Krisstank/Ender_3_Pro_v2_Max_SW_conversion/DXF/BLACK/top_rear_panel.dxf

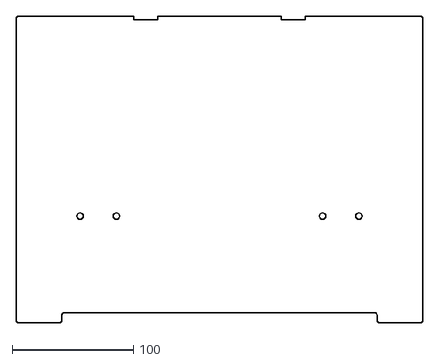
[picture p18: CAD file, 2023-01-02]
DXF/BLACK/top_rear_panel.dxf
336.0 x 253.0
