Krisstank/Ender_3_Pro_v2_Max_SW_conversion/DXF/CLEAR/front_side_clear_x2.dxf

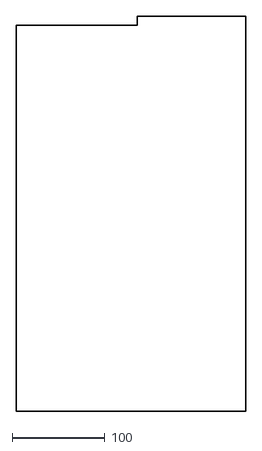
[picture p19: CAD file, 2023-01-02]
DXF/CLEAR/front_side_clear_x2.dxf
247.0 x 426.0
