Krisstank/Ender_3_Pro_v2_Max_SW_conversion/STL/Electronics/LCD/Mini12864/mount_mini12864.stl

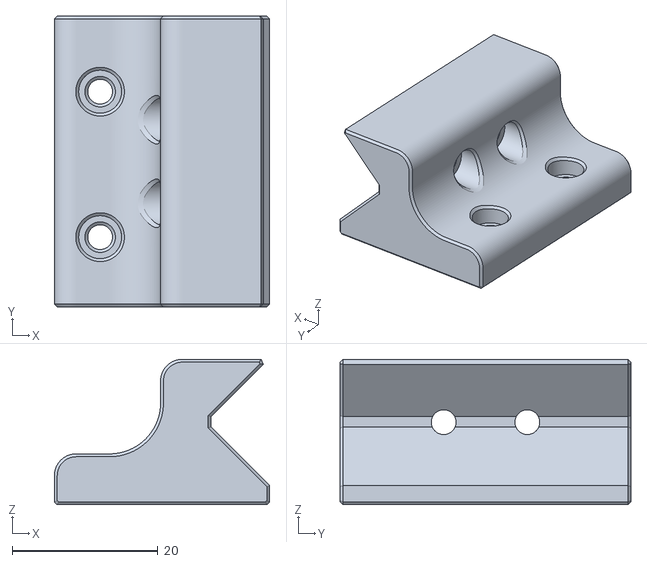
[picture p20: CAD file, 2023-01-02]
STL/Electronics/LCD/Mini12864/mount_mini12864.stl
29.6 x 40.0 x 20.0
