Krisstank/Ender_3_Pro_v2_Max_SW_conversion/STL/Electronics/rpi3_mount.stl

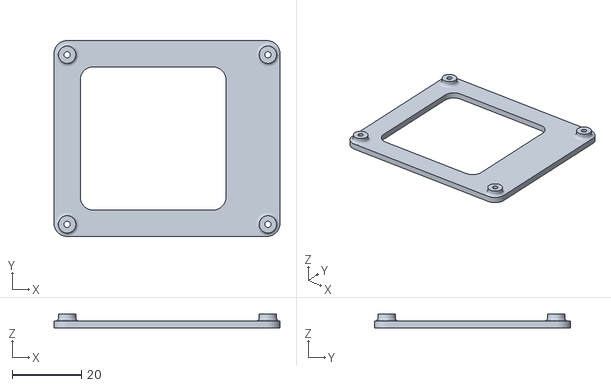
[picture p21: CAD file, 2023-01-02]
STL/Electronics/rpi3_mount.stl
65.3 x 56.6 x 4.00
