Krisstank/Ender_3_Pro_v2_Max_SW_conversion/STL/Gantry/XZ_Axis/XZ_Axis_Max/x_motor_mount_a_max.stl

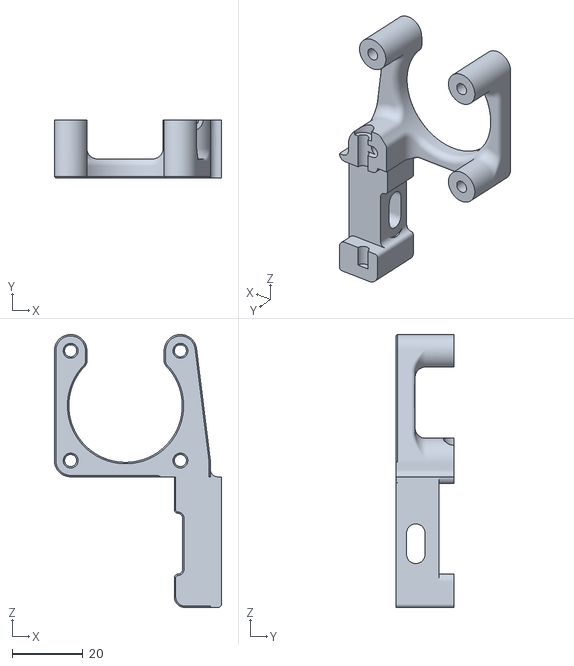
[picture p22: CAD file, 2023-01-02]
STL/Gantry/XZ_Axis/XZ_Axis_Max/x_motor_mount_a_max.stl
47.2 x 16.4 x 77.1
