Krisstank/Ender_3_Pro_v2_Max_SW_conversion/STL/Gantry/XZ_Axis/xz_block_right_b.stl

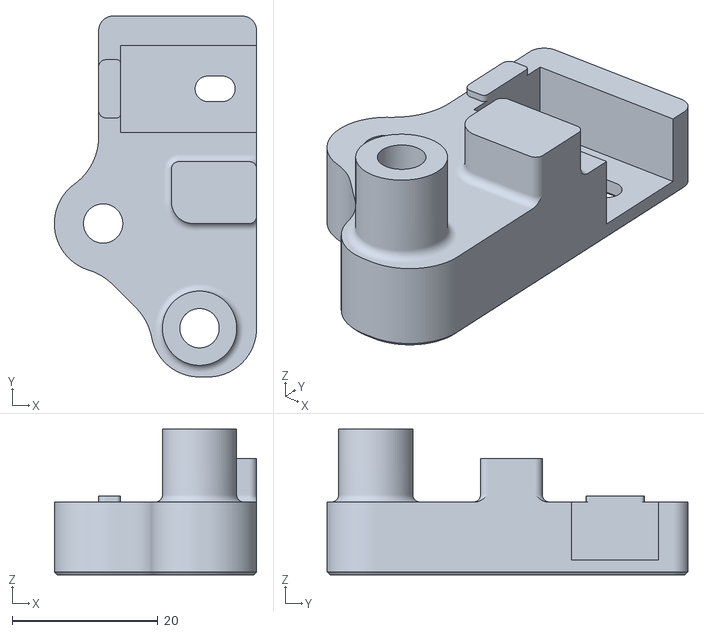
[picture p23: CAD file, 2023-01-02]
STL/Gantry/XZ_Axis/xz_block_right_b.stl
27.8 x 49.6 x 20.0
