Krisstank/Ender_3_Pro_v2_Max_SW_conversion/STL/Gantry/Y_Axis/[a]_y_chain_frame_mount_igus.stl

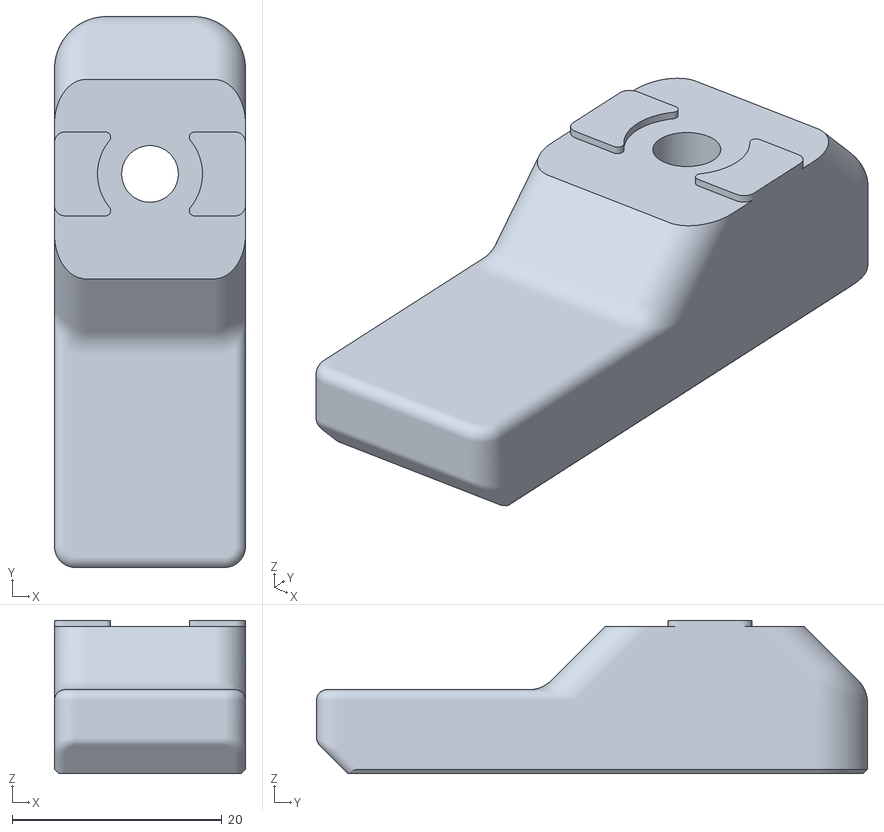
[picture p24: CAD file, 2023-01-02]
STL/Gantry/Y_Axis/[a]_y_chain_frame_mount_igus.stl
18.2 x 52.5 x 14.6
