Krisstank/Ender_3_Pro_v2_Max_SW_conversion/STL/Grills/[a]_grill_endcap_x4.stl

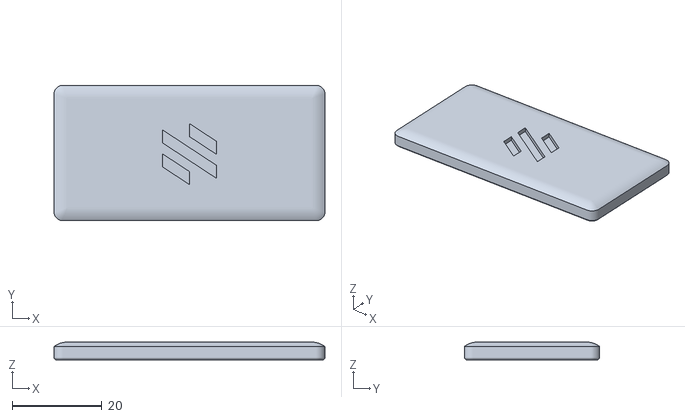
[picture p25: CAD file, 2023-01-02]
STL/Grills/[a]_grill_endcap_x4.stl
60.4 x 30.2 x 4.00
