Krisstank/Ender_3_Pro_v2_Max_SW_conversion/STL/Panel_Mounting/Doors/door_hinge_x4.stl

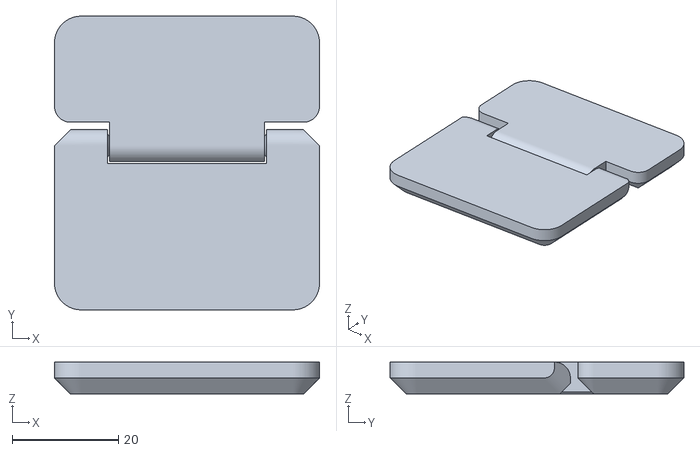
[picture p26: CAD file, 2023-01-02]
STL/Panel_Mounting/Doors/door_hinge_x4.stl
50.0 x 55.4 x 6.00
