Krisstank/Ender_3_Pro_v2_Max_SW_conversion/STL/Panel_Mounting/front_panel_bracket_a_x2.stl

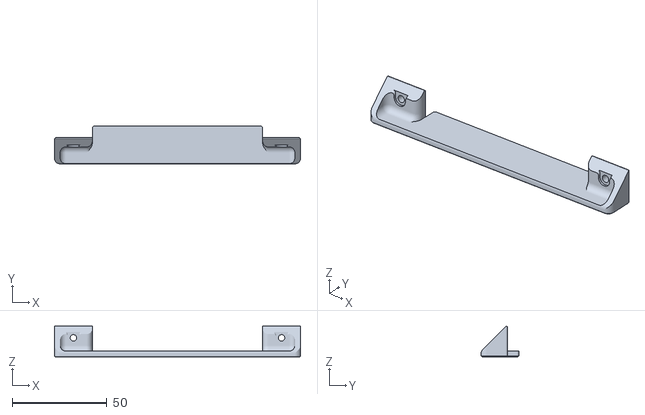
[picture p27: CAD file, 2023-01-02]
STL/Panel_Mounting/front_panel_bracket_a_x2.stl
130.0 x 20.0 x 16.2
