Krisstank/Ender_3_Pro_v2_Max_SW_conversion/STL/spool_holder.stl

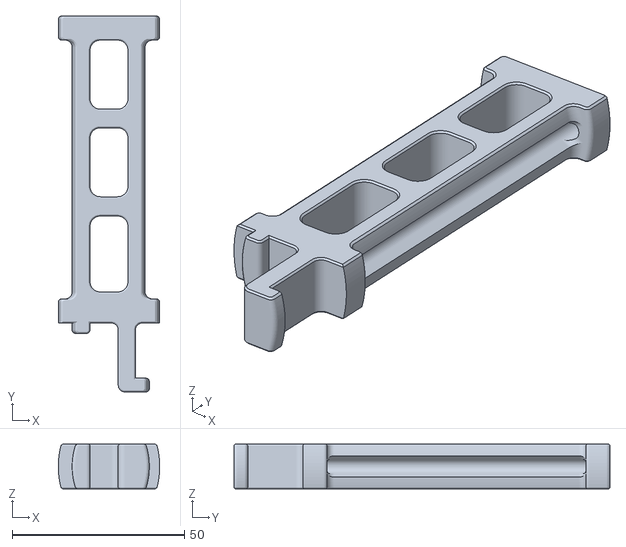
[picture p28: CAD file, 2023-01-02]
STL/spool_holder.stl
29.4 x 109.0 x 13.0
