Krisstank/Ender_3_Pro_v2_Max_SW_conversion/DXF/BLACK/rear_side_panel_x2.dxf

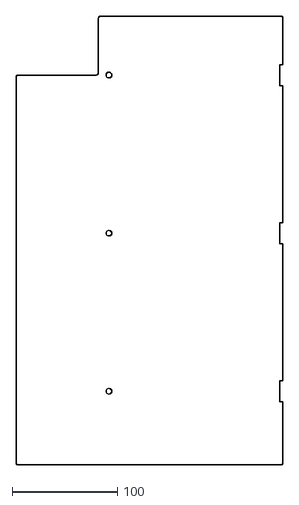
[picture p29: CAD file, 2023-01-02]
DXF/BLACK/rear_side_panel_x2.dxf
253.0 x 426.0
