Krisstank/Ender_3_Pro_v2_Max_SW_conversion/DXF/CLEAR/front_clear_door_x2.dxf

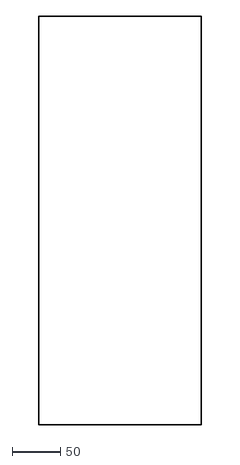
[picture p30: CAD file, 2023-01-02]
DXF/CLEAR/front_clear_door_x2.dxf
168.0 x 422.0
