Krisstank/Ender_3_Pro_v2_Max_SW_conversion/STL/Decks/front_left.stl

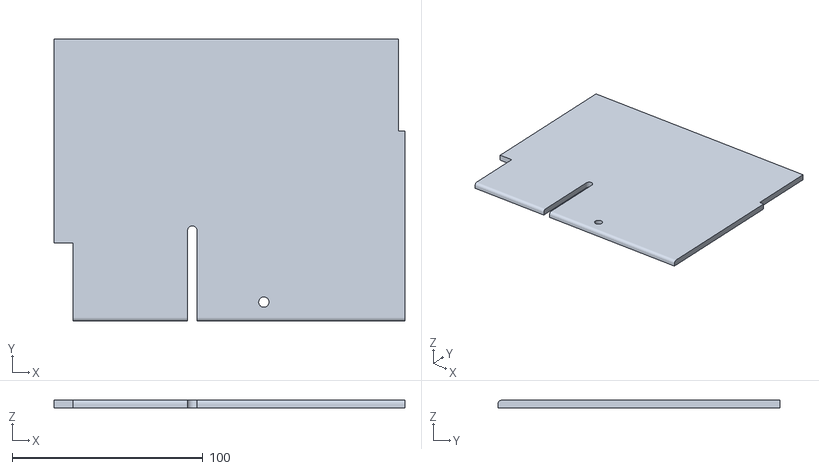
[picture p31: CAD file, 2023-01-02]
STL/Decks/front_left.stl
184.0 x 148.0 x 4.00
