Krisstank/Ender_3_Pro_v2_Max_SW_conversion/STL/Electronics/LCD/Mini12864/lcd_case_rear_mini12864.stl

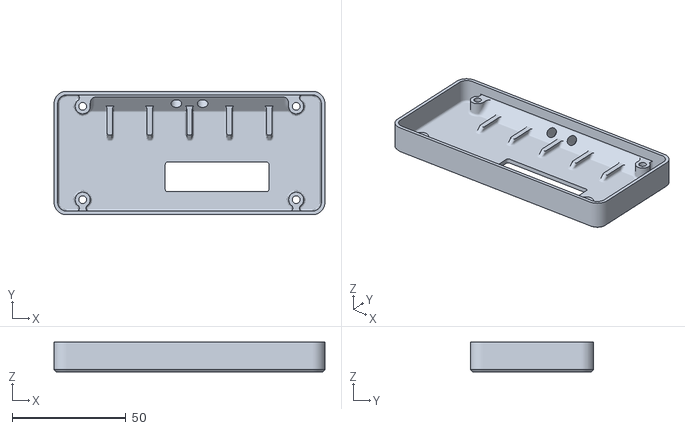
[picture p32: CAD file, 2023-01-02]
STL/Electronics/LCD/Mini12864/lcd_case_rear_mini12864.stl
119.0 x 54.2 x 13.0
