Krisstank/Ender_3_Pro_v2_Max_SW_conversion/STL/Electronics/PS_4040_mount_b.stl

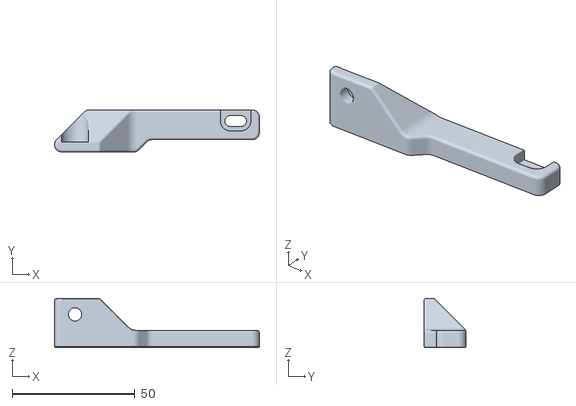
[picture p33: CAD file, 2023-01-02]
STL/Electronics/PS_4040_mount_b.stl
83.4 x 17.1 x 20.0
