Krisstank/Ender_3_Pro_v2_Max_SW_conversion/STL/foot_tpu_x4.stl

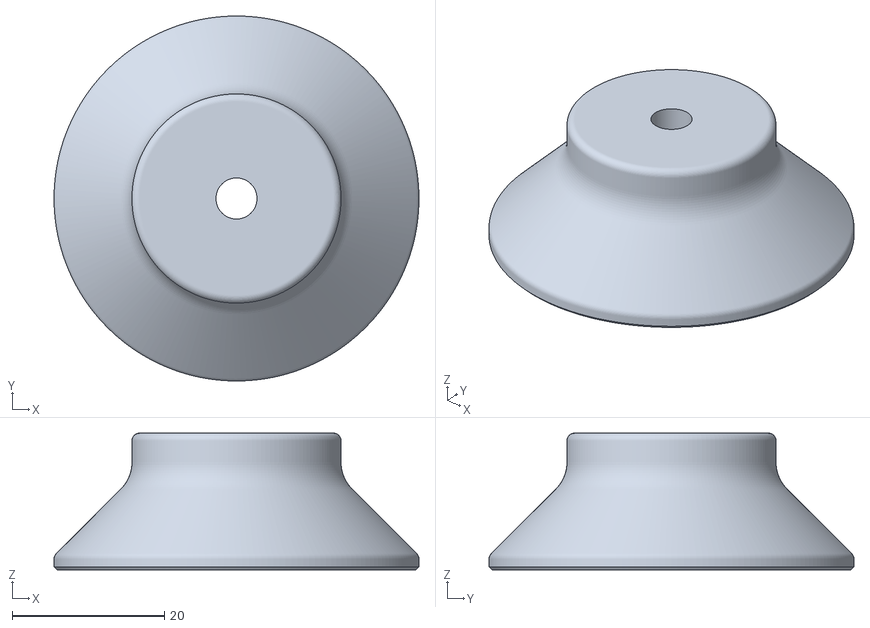
[picture p34: CAD file, 2023-01-02]
STL/foot_tpu_x4.stl
48.0 x 48.0 x 18.0
