Krisstank/Ender_3_Pro_v2_Max_SW_conversion/STL/Gantry/XZ_Axis/keybak_idler_bracket.stl

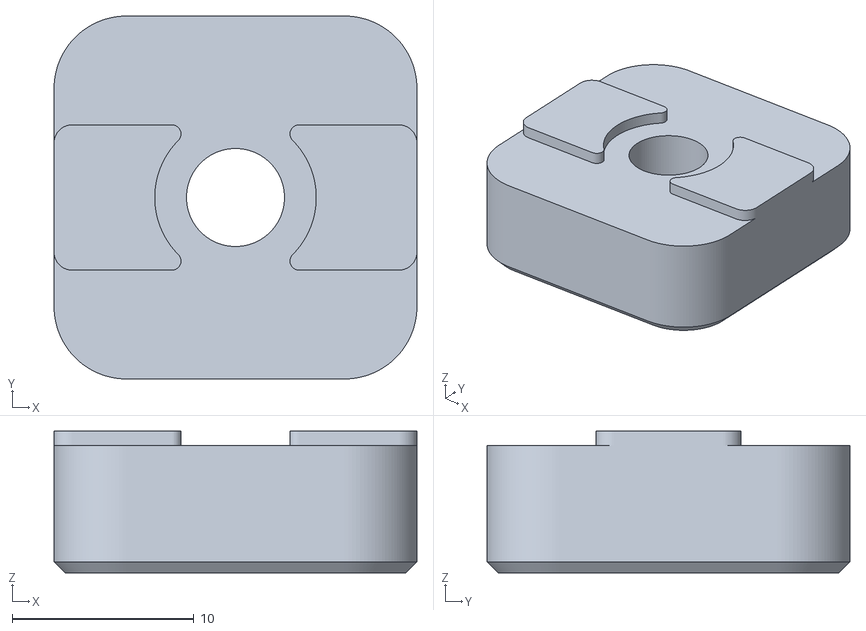
[picture p35: CAD file, 2023-01-02]
STL/Gantry/XZ_Axis/keybak_idler_bracket.stl
20.0 x 20.0 x 7.80
