Krisstank/Ender_3_Pro_v2_Max_SW_conversion/STL/Gantry/XZ_Axis/XZ_Axis_Max/z_motor_mount_b_max.stl

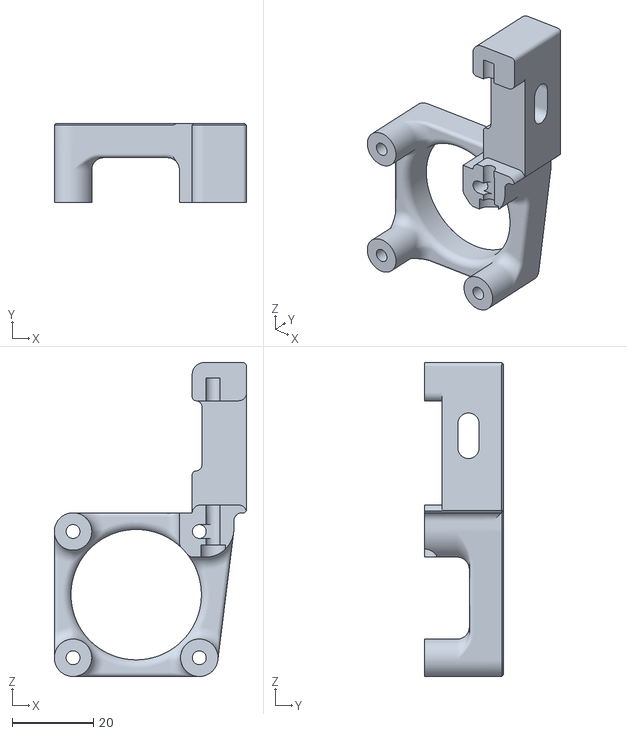
[picture p36: CAD file, 2023-01-02]
STL/Gantry/XZ_Axis/XZ_Axis_Max/z_motor_mount_b_max.stl
47.2 x 19.4 x 77.1
