Krisstank/Ender_3_Pro_v2_Max_SW_conversion/STL/Gantry/Y_Axis/[a]_y_idler_outter.stl

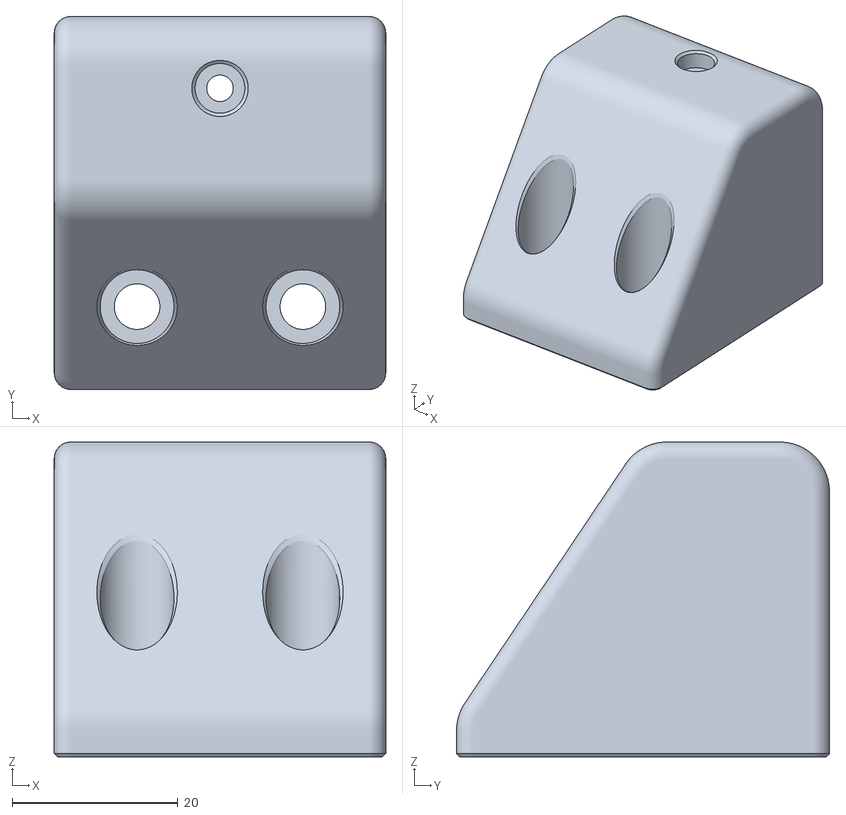
[picture p37: CAD file, 2023-01-02]
STL/Gantry/Y_Axis/[a]_y_idler_outter.stl
40.0 x 45.0 x 38.0
