Krisstank/Ender_3_Pro_v2_Max_SW_conversion/STL/Grills/grill_front_middle.stl

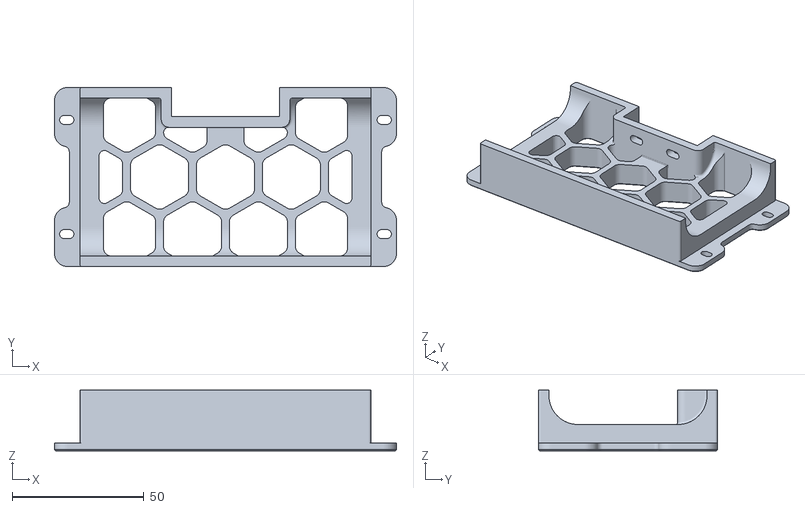
[picture p38: CAD file, 2023-01-02]
STL/Grills/grill_front_middle.stl
129.8 x 68.0 x 23.0
