Krisstank/Ender_3_Pro_v2_Max_SW_conversion/STL/Panel_Mounting/panel_clip_x4.stl

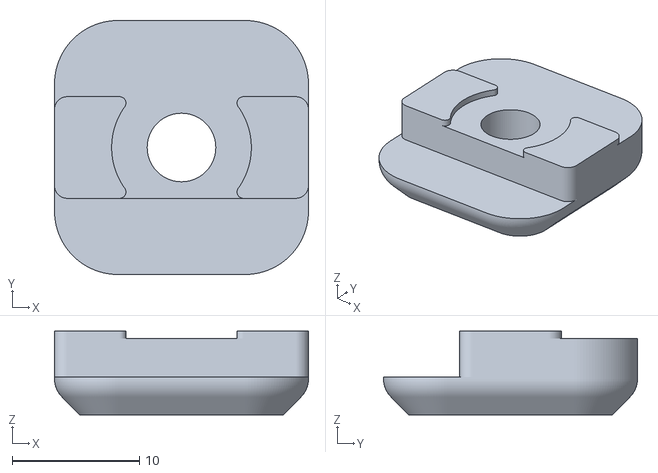
[picture p39: CAD file, 2023-01-02]
STL/Panel_Mounting/panel_clip_x4.stl
20.0 x 20.0 x 6.60
