Krisstank/Ender_3_Pro_v2_Max_SW_conversion/DXF/BLACK/deck_right.dxf

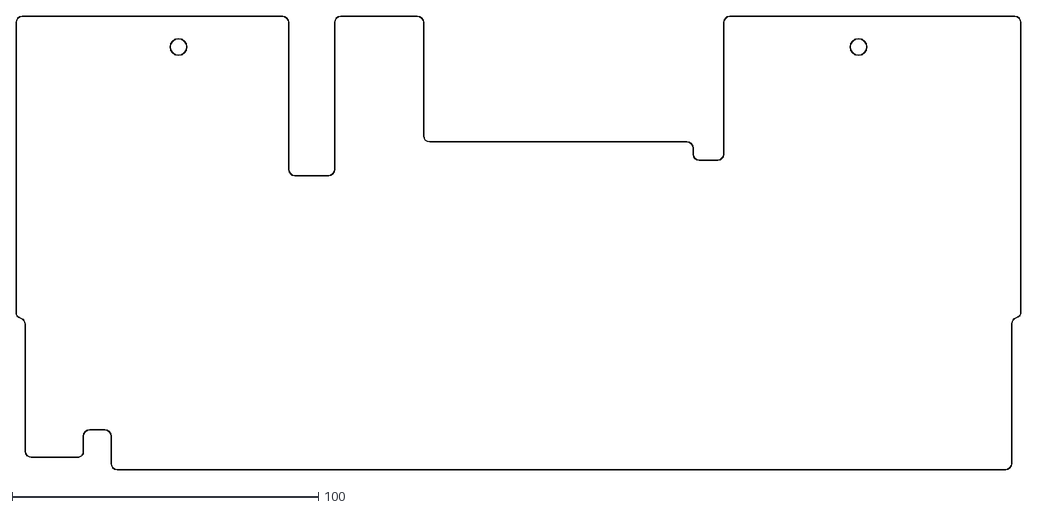
[picture p40: CAD file, 2023-01-02]
DXF/BLACK/deck_right.dxf
328.0 x 148.0
