Krisstank/Ender_3_Pro_v2_Max_SW_conversion/STL/Gantry/XZ_Axis/[a]_upper_idler_support_b_right.stl

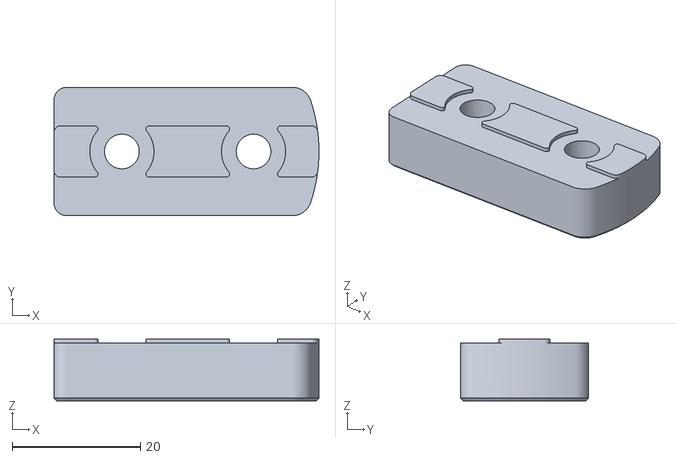
[picture p42: CAD file, 2023-01-02]
STL/Gantry/XZ_Axis/[a]_upper_idler_support_b_right.stl
41.3 x 20.0 x 9.60
