Krisstank/Ender_3_Pro_v2_Max_SW_conversion/STL/Gantry/Y_Axis/[a]_y_chain_bed_mount_generic.stl

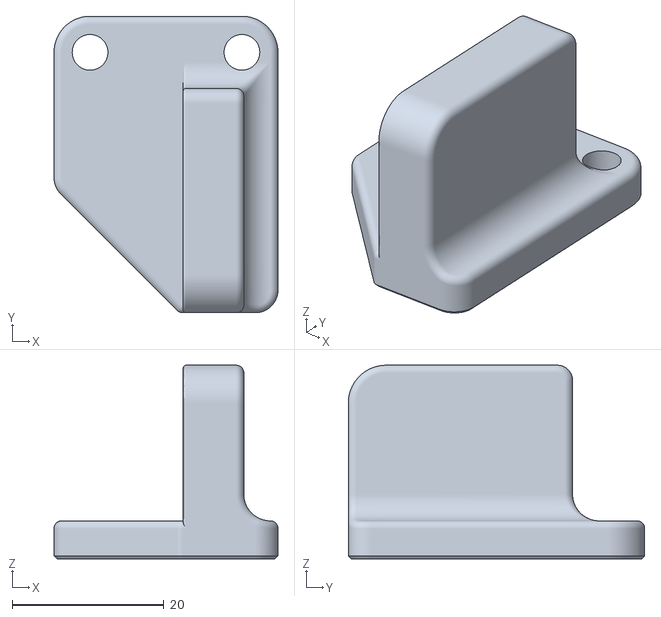
[picture p43: CAD file, 2023-01-02]
STL/Gantry/Y_Axis/[a]_y_chain_bed_mount_generic.stl
29.5 x 39.0 x 25.5
