Krisstank/Ender_3_Pro_v2_Max_SW_conversion/STL/Panel_Mounting/rear_panel_bracket_x5.stl

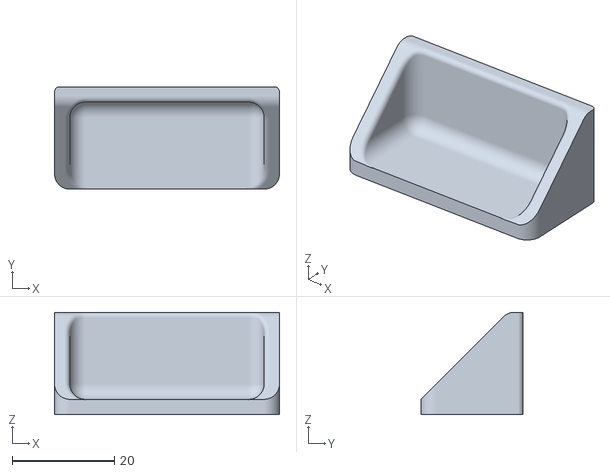
[picture p44: CAD file, 2023-01-02]
STL/Panel_Mounting/rear_panel_bracket_x5.stl
44.0 x 20.0 x 20.0
