Krisstank/Ender_3_Pro_v2_Max_SW_conversion/DXF/BLACK/rear_panel.dxf

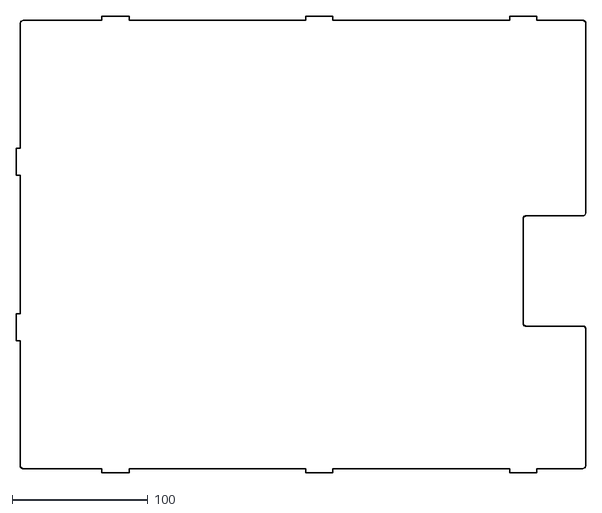
[picture p45: CAD file, 2023-01-02]
DXF/BLACK/rear_panel.dxf
419.0 x 336.0
