Krisstank/Ender_3_Pro_v2_Max_SW_conversion/STL/Electronics/rpi3_shelf.stl

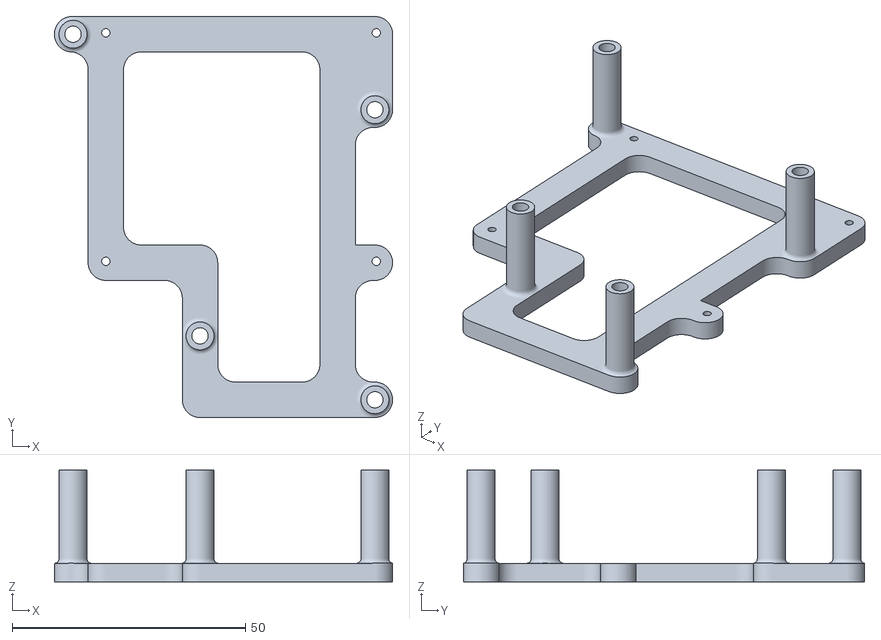
[picture p46: CAD file, 2023-01-02]
STL/Electronics/rpi3_shelf.stl
72.5 x 86.0 x 24.0
