Krisstank/Ender_3_Pro_v2_Max_SW_conversion/STL/frame_extension_x2_max.stl

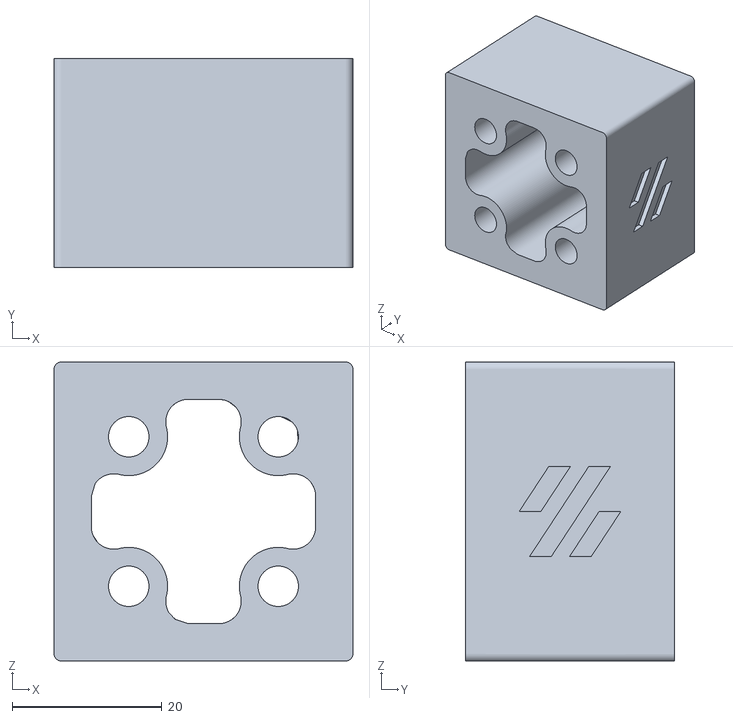
[picture p47: CAD file, 2023-01-02]
STL/frame_extension_x2_max.stl
40.0 x 28.0 x 40.0
