Krisstank/Ender_3_Pro_v2_Max_SW_conversion/STL/Gantry/XZ_Axis/[a]_xz_cable_cover.stl

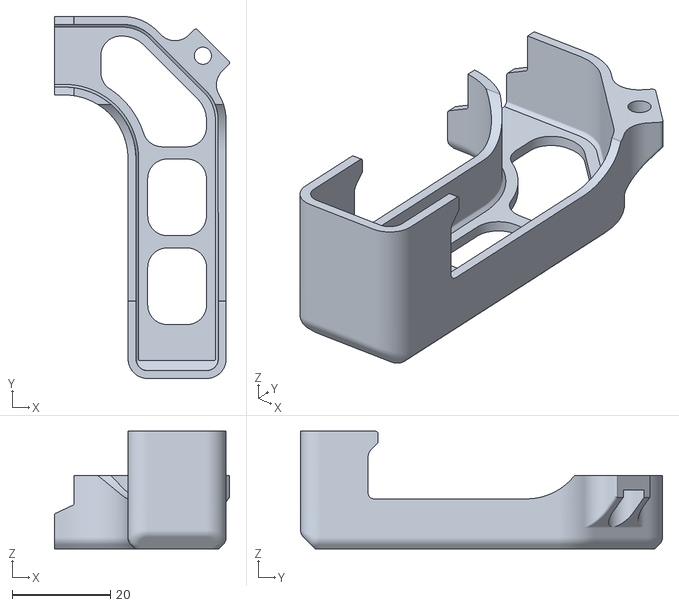
[picture p48: CAD file, 2023-01-02]
STL/Gantry/XZ_Axis/[a]_xz_cable_cover.stl
35.7 x 73.8 x 24.0
