Krisstank/Ender_3_Pro_v2_Max_SW_conversion/STL/Gantry/Y_Axis/[a]_y_axis_ls_mount.stl

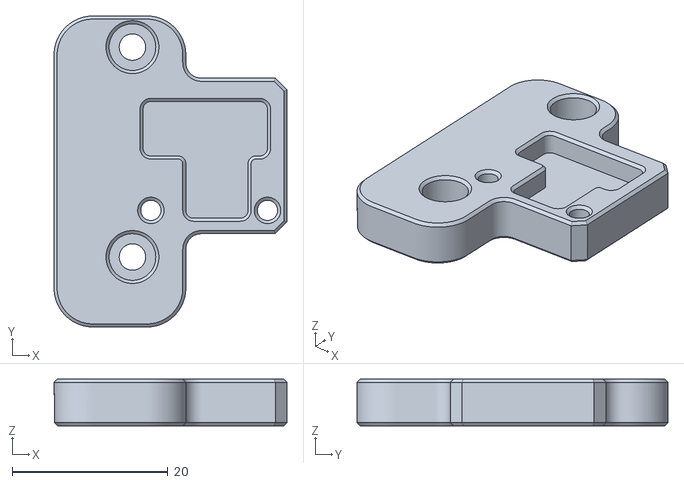
[picture p49: CAD file, 2023-01-02]
STL/Gantry/Y_Axis/[a]_y_axis_ls_mount.stl
30.0 x 40.0 x 6.00
