Krisstank/Ender_3_Pro_v2_Max_SW_conversion/STL/Grills/grill_rear_right.stl

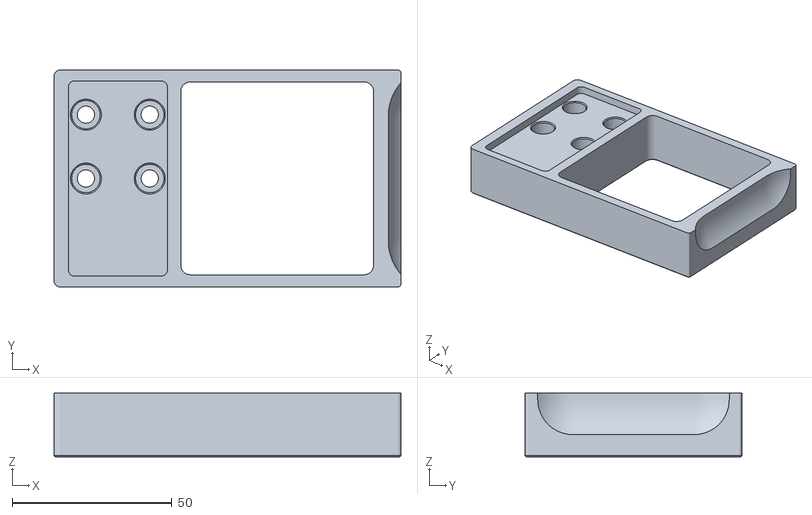
[picture p50: CAD file, 2023-01-02]
STL/Grills/grill_rear_right.stl
108.7 x 68.0 x 20.0
