Krisstank/Ender_3_Pro_v2_Max_SW_conversion/DXF/BLACK/front_bottom_panel.dxf

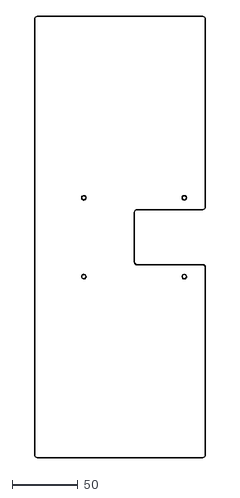
[picture p52: CAD file, 2023-01-02]
DXF/BLACK/front_bottom_panel.dxf
130.0 x 336.0
