Krisstank/Ender_3_Pro_v2_Max_SW_conversion/STL/Electronics/rs_25_mount.stl

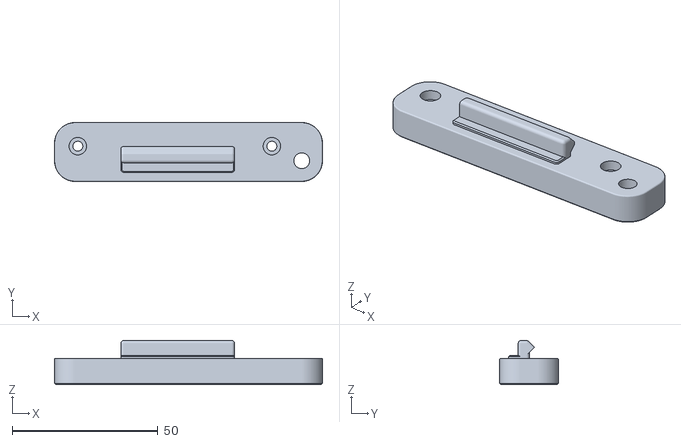
[picture p53: CAD file, 2023-01-02]
STL/Electronics/rs_25_mount.stl
91.9 x 20.2 x 15.1
