Krisstank/Ender_3_Pro_v2_Max_SW_conversion/STL/Gantry/Y_Axis/[a]_y_belt_clip_x2.stl

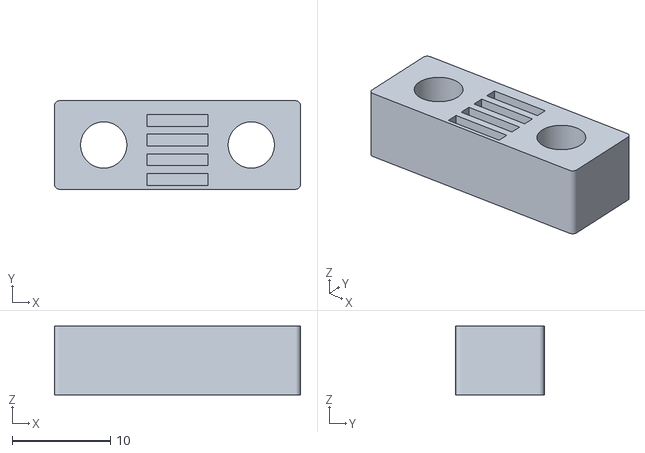
[picture p55: CAD file, 2023-01-02]
STL/Gantry/Y_Axis/[a]_y_belt_clip_x2.stl
25.0 x 9.00 x 7.00
