Krisstank/Ender_3_Pro_v2_Max_SW_conversion/STL/Panel_Mounting/front_bottom_panel_bracket.stl

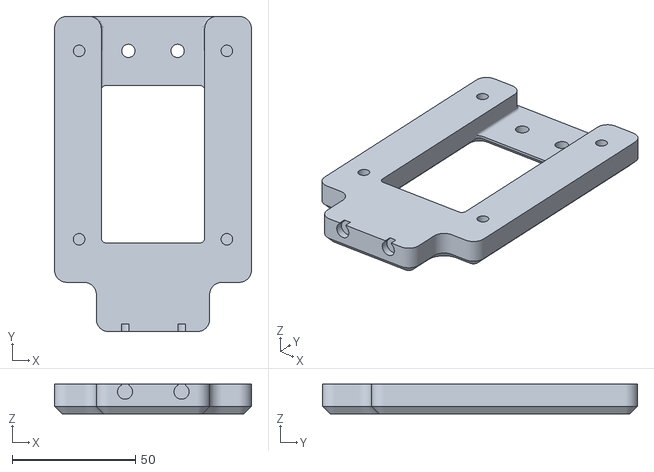
[picture p56: CAD file, 2023-01-02]
STL/Panel_Mounting/front_bottom_panel_bracket.stl
80.0 x 128.0 x 12.0
