Krisstank/Ender_3_Pro_v2_Max_SW_conversion/STL/spool_holder_base.stl

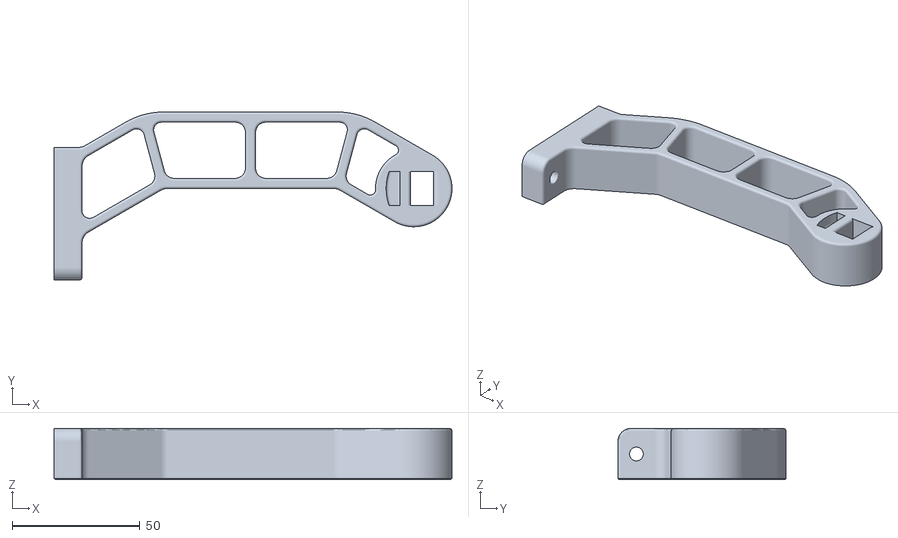
[picture p57: CAD file, 2023-01-02]
STL/spool_holder_base.stl
156.0 x 65.9 x 20.0
