Krisstank/Ender_3_Pro_v2_Max_SW_conversion/STL/Electronics/skr_mini_e3_mount.stl

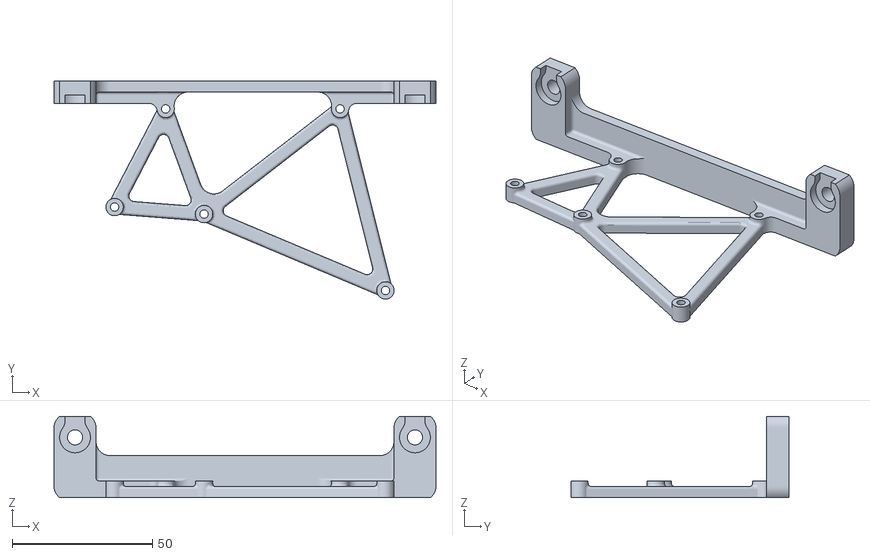
[picture p58: CAD file, 2023-01-02]
STL/Electronics/skr_mini_e3_mount.stl
136.2 x 77.8 x 29.0
