Krisstank/Ender_3_Pro_v2_Max_SW_conversion/STL/foot_extention_x4.stl

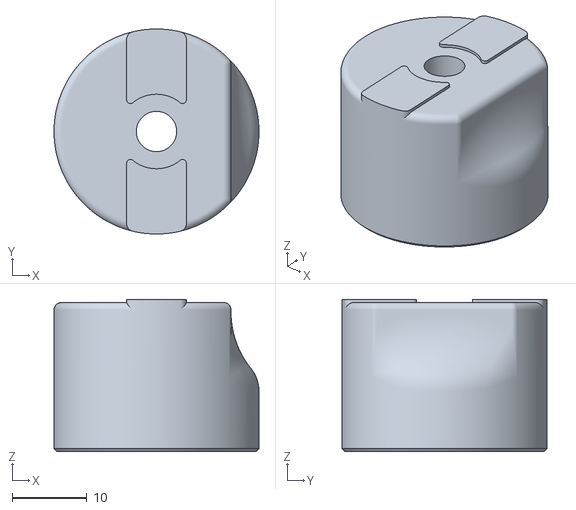
[picture p59: CAD file, 2023-01-02]
STL/foot_extention_x4.stl
27.5 x 27.5 x 20.4
