Krisstank/Ender_3_Pro_v2_Max_SW_conversion/STL/Gantry/XZ_Axis/z_bearing_block_left.stl

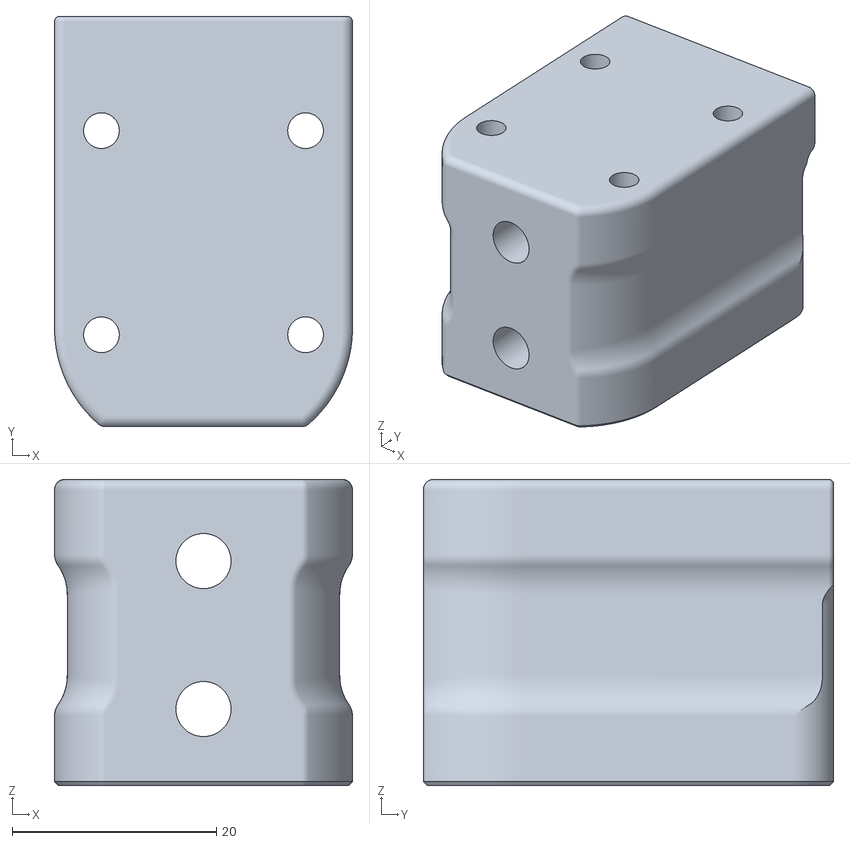
[picture p60: CAD file, 2023-01-02]
STL/Gantry/XZ_Axis/z_bearing_block_left.stl
29.2 x 40.2 x 30.0
