Krisstank/Ender_3_Pro_v2_Max_SW_conversion/STL/Gantry/Y_Axis/[a]_y_idler_inner.stl

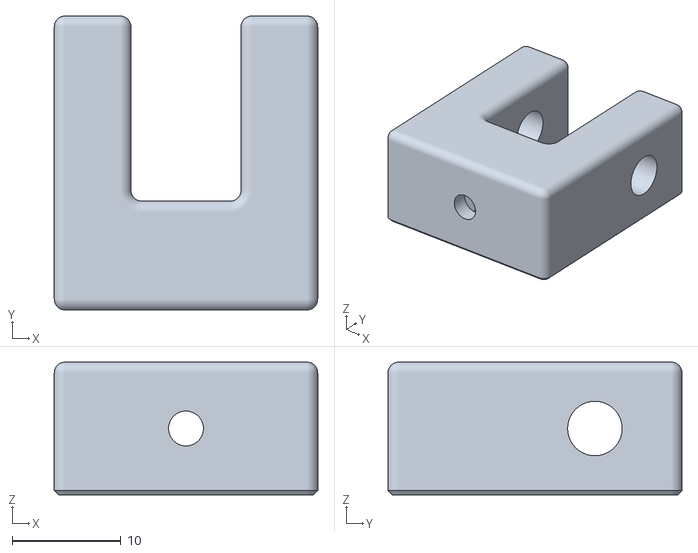
[picture p61: CAD file, 2023-01-02]
STL/Gantry/Y_Axis/[a]_y_idler_inner.stl
24.2 x 27.0 x 12.2
