Krisstank/Ender_3_Pro_v2_Max_SW_conversion/STL/Panel_Mounting/light_bar_x2.stl

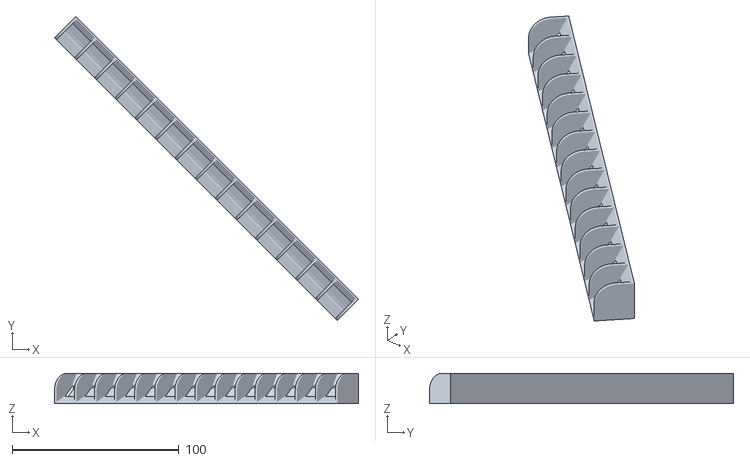
[picture p62: CAD file, 2023-01-02]
STL/Panel_Mounting/light_bar_x2.stl
182.2 x 182.2 x 18.0
