Krisstank/Ender_3_Pro_v2_Max_SW_conversion/STL/cover_4040_extrusion_cut_enderV2.stl

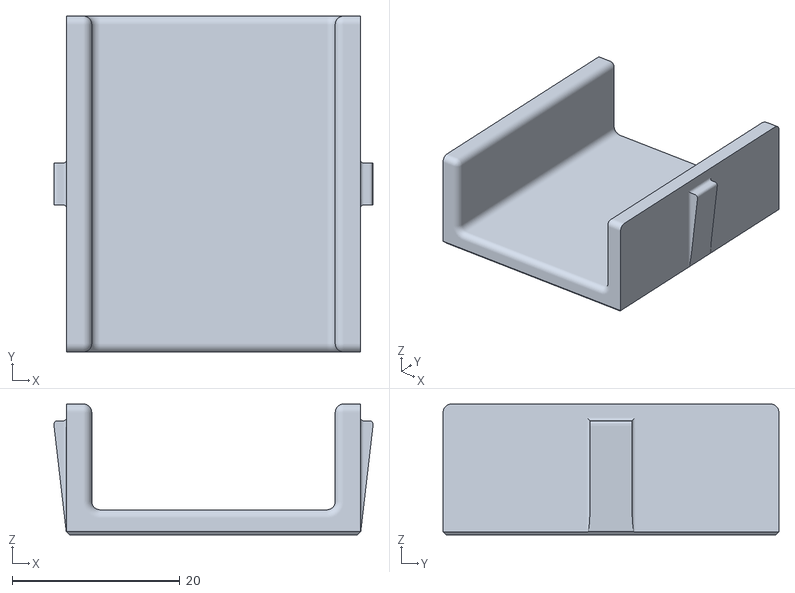
[picture p63: CAD file, 2023-01-02]
STL/cover_4040_extrusion_cut_enderV2.stl
38.0 x 40.0 x 15.6
