Krisstank/Ender_3_Pro_v2_Max_SW_conversion/STL/Gantry/Y_Axis/y_motor_mount_a.stl

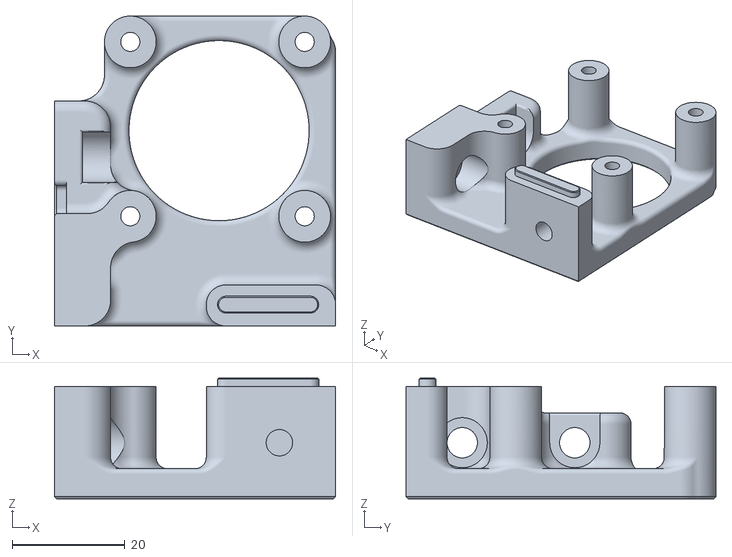
[picture p65: CAD file, 2023-01-02]
STL/Gantry/Y_Axis/y_motor_mount_a.stl
50.0 x 55.1 x 21.5
