Krisstank/Ender_3_Pro_v2_Max_SW_conversion/STL/Panel_Mounting/panel_clip_wide_x2.stl

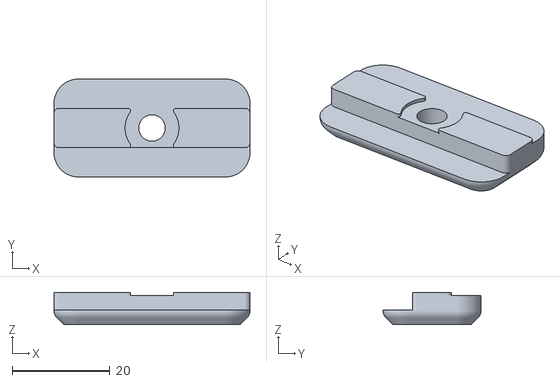
[picture p66: CAD file, 2023-01-02]
STL/Panel_Mounting/panel_clip_wide_x2.stl
40.0 x 20.0 x 6.60
