Krisstank/Ender_3_Pro_v2_Max_SW_conversion/STL/Gantry/XZ_Axis/z_carriage_stop_bottom_x2.stl

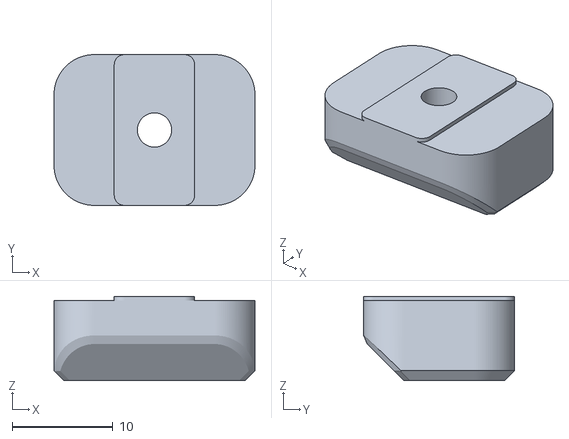
[picture p67: CAD file, 2023-01-02]
STL/Gantry/XZ_Axis/z_carriage_stop_bottom_x2.stl
20.0 x 15.0 x 8.40
