Krisstank/Ender_3_Pro_v2_Max_SW_conversion/STL/Panel_Mounting/top_door_latch.stl

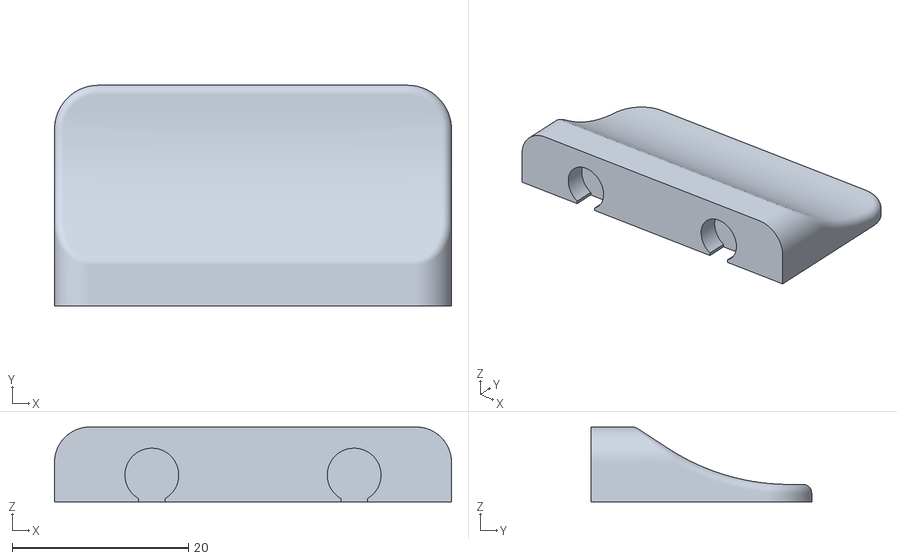
[picture p69: CAD file, 2023-01-02]
STL/Panel_Mounting/top_door_latch.stl
45.0 x 25.0 x 8.50
