Krisstank/Ender_3_Pro_v2_Max_SW_conversion/STL/Gantry/Y_Axis/y_axis_Ender3_Max_CR10_bed_carriage.stl

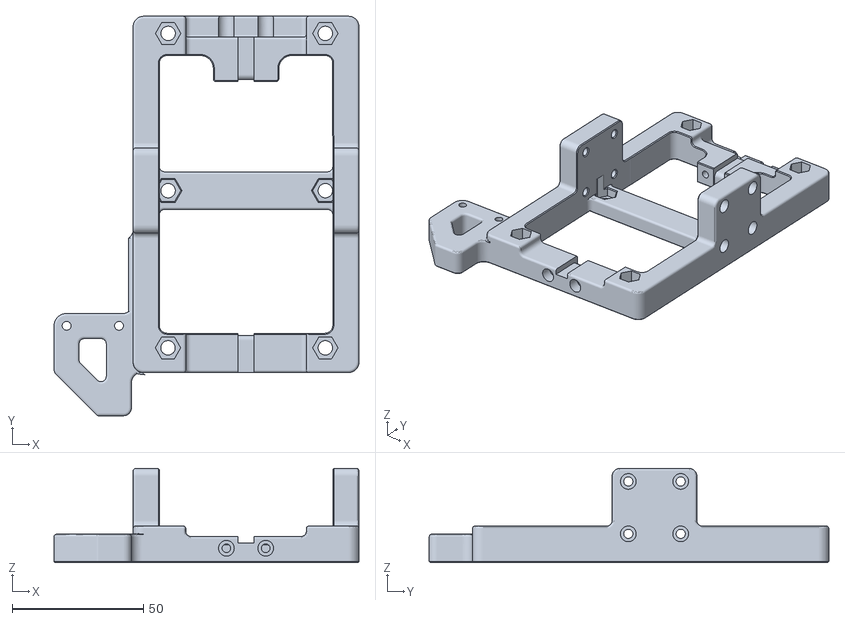
[picture p70: CAD file, 2023-01-02]
STL/Gantry/Y_Axis/y_axis_Ender3_Max_CR10_bed_carriage.stl
116.4 x 152.5 x 36.0
