Krisstank/Ender_3_Pro_v2_Max_SW_conversion/STL/Panel_Mounting/feed_slot.stl

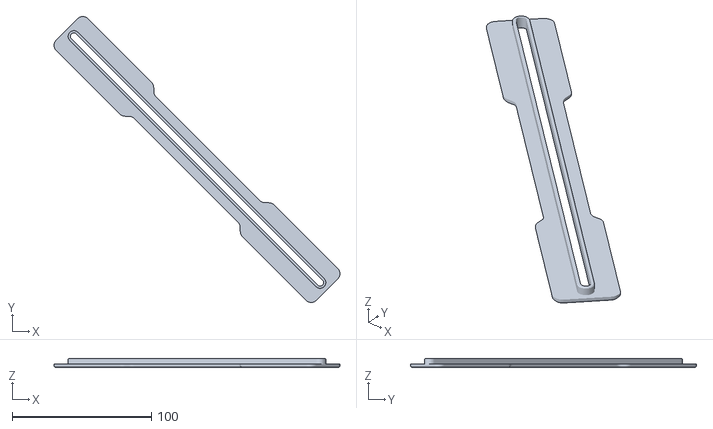
[picture p71: CAD file, 2023-01-02]
STL/Panel_Mounting/feed_slot.stl
205.3 x 205.3 x 6.40
