Krisstank/Ender_3_Pro_v2_Max_SW_conversion/STL/Gantry/Y_Axis/y_motor_mount_b.stl

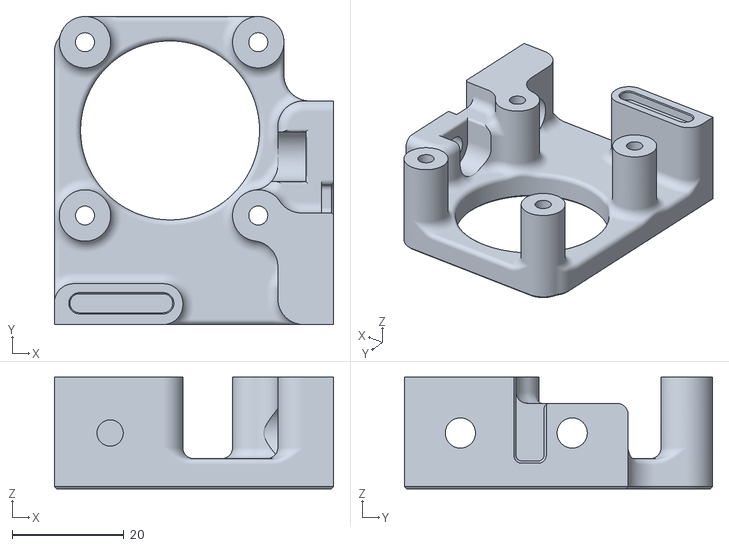
[picture p72: CAD file, 2023-01-02]
STL/Gantry/Y_Axis/y_motor_mount_b.stl
50.0 x 55.1 x 20.0
