Krisstank/Ender_3_Pro_v2_Max_SW_conversion/STL/Gantry/XZ_Axis/keybak_mount.stl

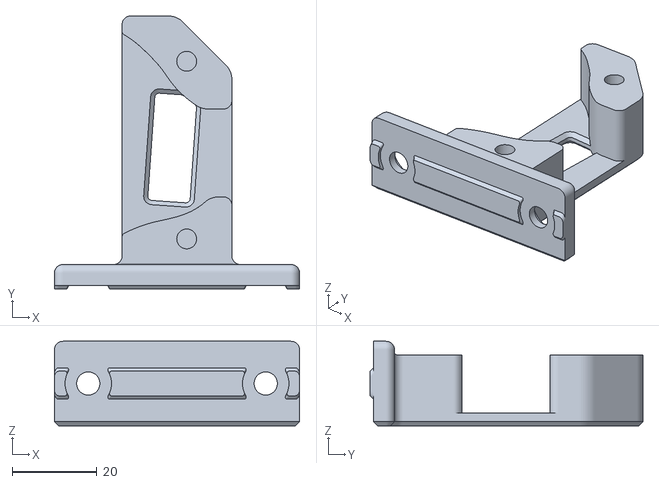
[picture p73: CAD file, 2023-01-02]
STL/Gantry/XZ_Axis/keybak_mount.stl
58.0 x 64.6 x 20.0
