Krisstank/Ender_3_Pro_v2_Max_SW_conversion/STL/Gantry/Y_Axis/y_axis_bed_carriage.stl

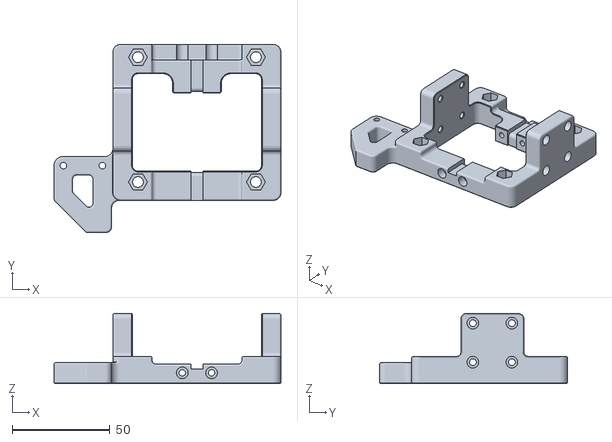
[picture p74: CAD file, 2023-01-02]
STL/Gantry/Y_Axis/y_axis_bed_carriage.stl
116.4 x 96.5 x 36.0
