Krisstank/Ender_3_Pro_v2_Max_SW_conversion/STL/Gantry/XZ_Axis/x_motor_mount_b.stl

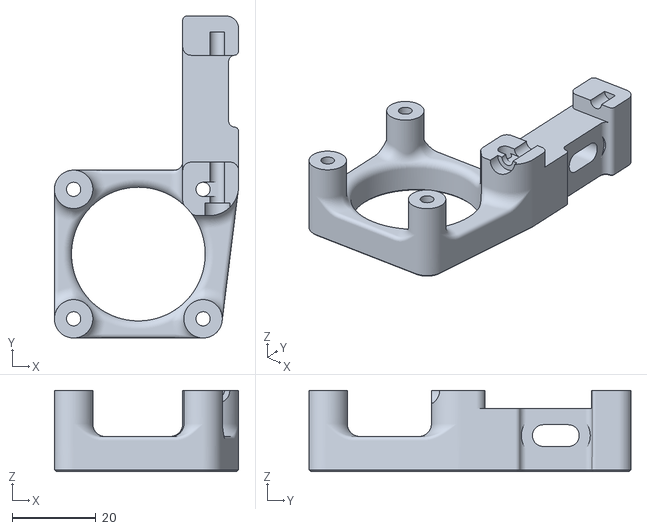
[picture p75: CAD file, 2023-01-02]
STL/Gantry/XZ_Axis/x_motor_mount_b.stl
44.1 x 77.1 x 19.4
