Krisstank/Ender_3_Pro_v2_Max_SW_conversion/STL/Gantry/XZ_Axis/z_bearing_block_right_igus.stl

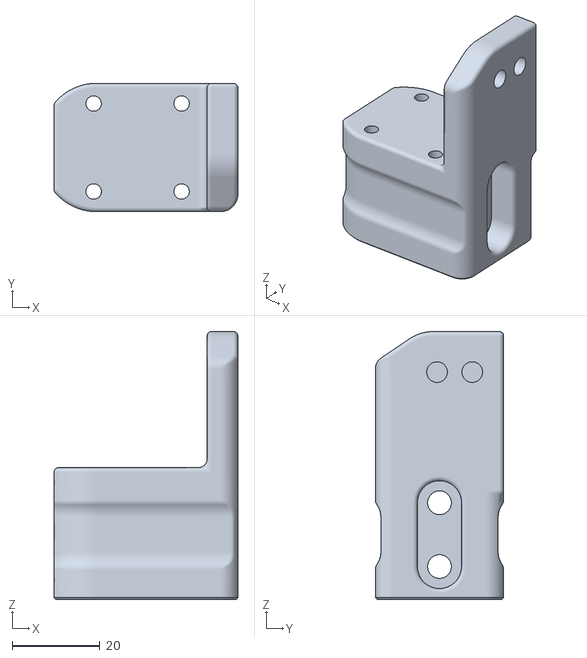
[picture p77: CAD file, 2023-01-02]
STL/Gantry/XZ_Axis/z_bearing_block_right_igus.stl
41.8 x 29.2 x 60.9
