Krisstank/Ender_3_Pro_v2_Max_SW_conversion/STL/Gantry/XZ_Axis/[a]_z_chain_lower_mount_generic.stl

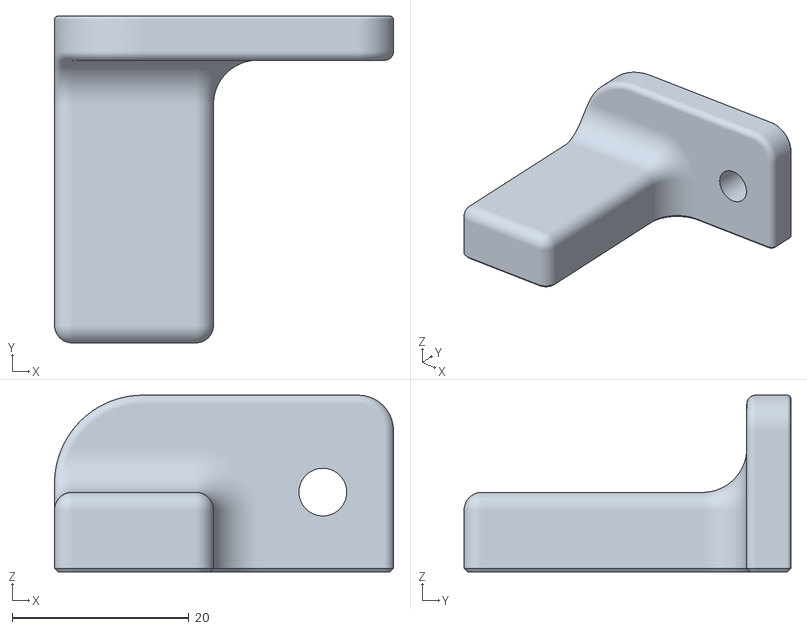
[picture p78: CAD file, 2023-01-02]
STL/Gantry/XZ_Axis/[a]_z_chain_lower_mount_generic.stl
38.4 x 37.0 x 20.0
