Krisstank/Ender_3_Pro_v2_Max_SW_conversion/STL/Gantry/XZ_Axis/[a]_upper_idler_support_b_left.3mf

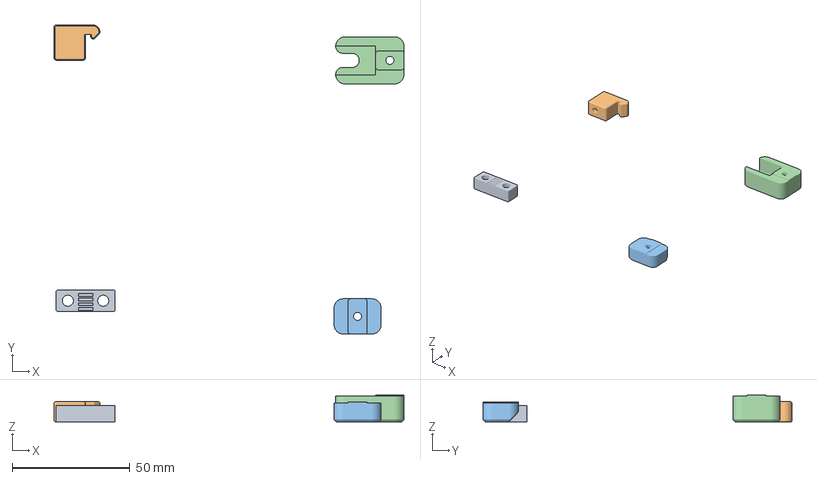
[picture p79: CAD file, 2023-01-02]
STL/Gantry/XZ_Axis/[a]_upper_idler_support_b_left.3mf
148.5 x 131.2 x 11.4 mm
[a]_y_belt_clip_x2.stl
[a]_xz_tensioner_x2.stl
z_carriage_stop_bottom_x2.stl
z_carriage_stop_top_x2.stl
