Krisstank/Ender_3_Pro_v2_Max_SW_conversion/STL/Gantry/XZ_Axis/keybak_gantry_anchor.stl

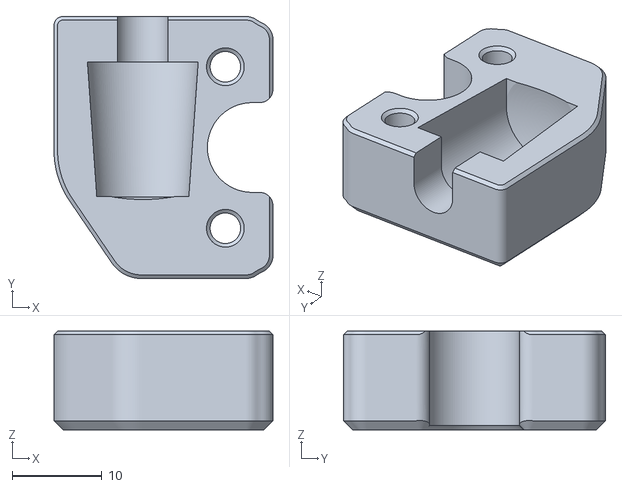
[picture p80: CAD file, 2023-01-02]
STL/Gantry/XZ_Axis/keybak_gantry_anchor.stl
24.4 x 29.2 x 11.0
