Krisstank/Ender_3_Pro_v2_Max_SW_conversion/STL/Gantry/XZ_Axis/keybak_mount_plate.stl

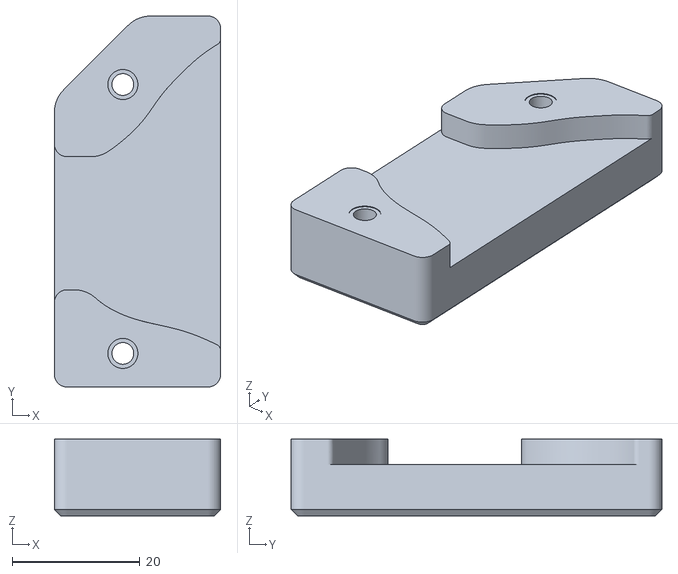
[picture p81: CAD file, 2023-01-02]
STL/Gantry/XZ_Axis/keybak_mount_plate.stl
26.0 x 58.0 x 12.0
