Krisstank/Ender_3_Pro_v2_Max_SW_conversion/STL/Gantry/XZ_Axis/[a]_xz_tensioner_x2.stl

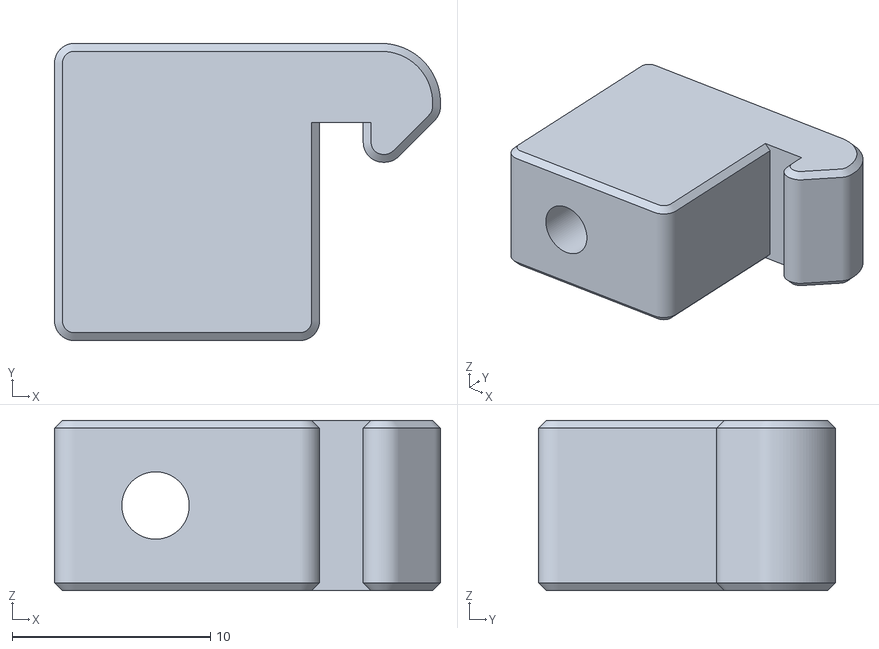
[picture p83: CAD file, 2023-01-02]
STL/Gantry/XZ_Axis/[a]_xz_tensioner_x2.stl
19.5 x 15.0 x 8.60
