Krisstank/Ender_3_Pro_v2_Max_SW_conversion/STL/Gantry/XZ_Axis/z_carriage_stop_top_x2.stl

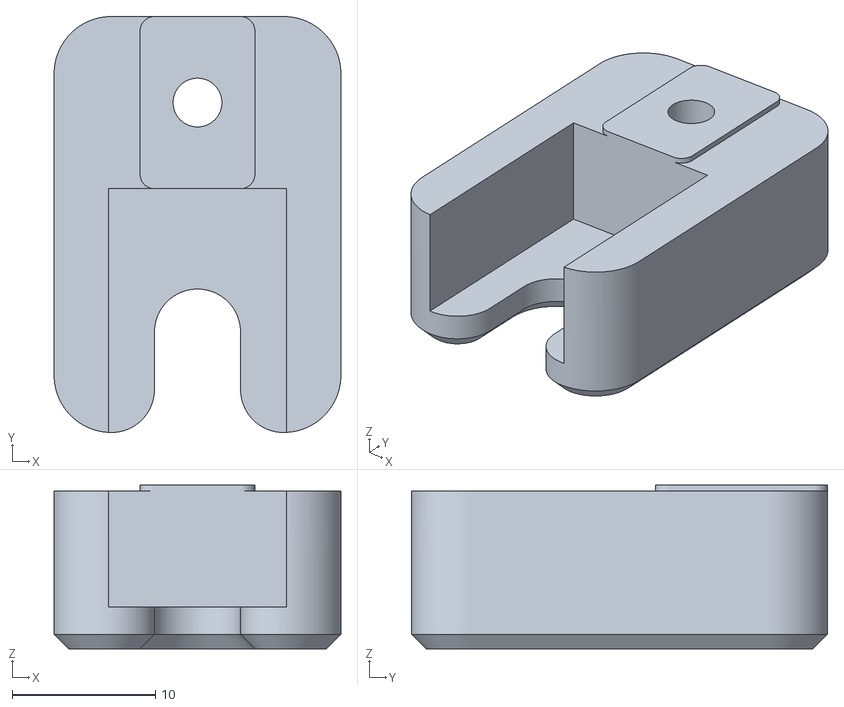
[picture p84: CAD file, 2023-01-02]
STL/Gantry/XZ_Axis/z_carriage_stop_top_x2.stl
20.0 x 29.0 x 11.4
